coelacant1/EpsilonProtogen/Pictures/1 (1).jpg

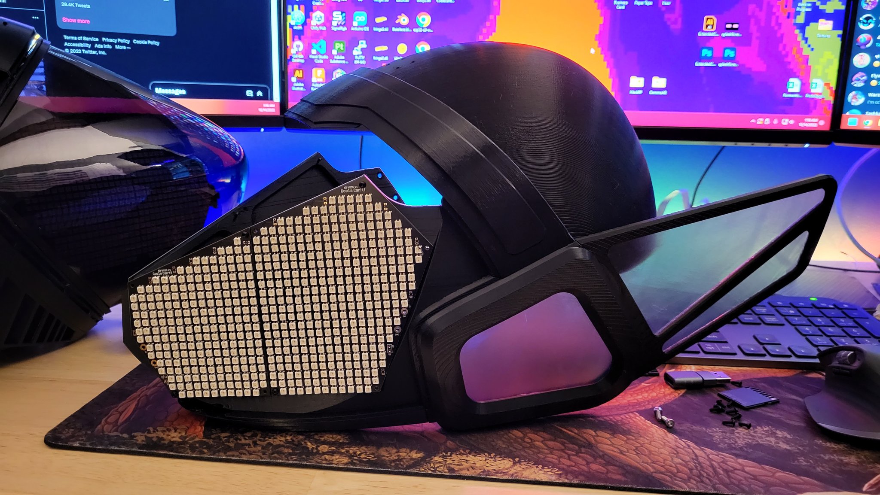
Pictures/1 (1).jpg
