coelacant1/EpsilonProtogen/Pictures/1 (2).jpg

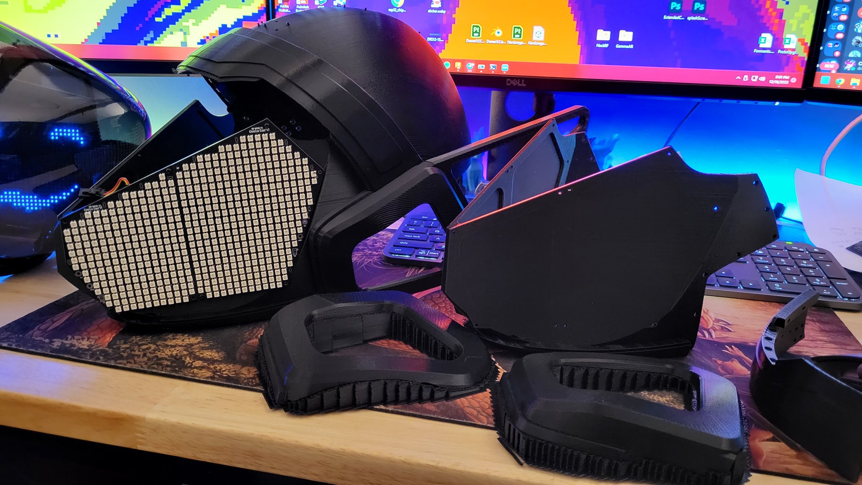
Pictures/1 (2).jpg
