coelacant1/EpsilonProtogen/Pictures/1 (3).jpg

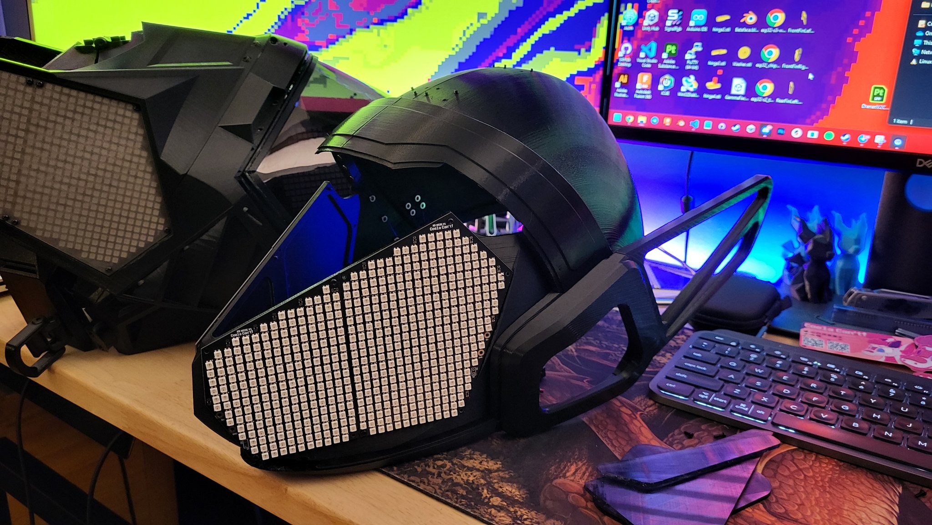
Pictures/1 (3).jpg
