coelacant1/EpsilonProtogen/Pictures/Bottom.png

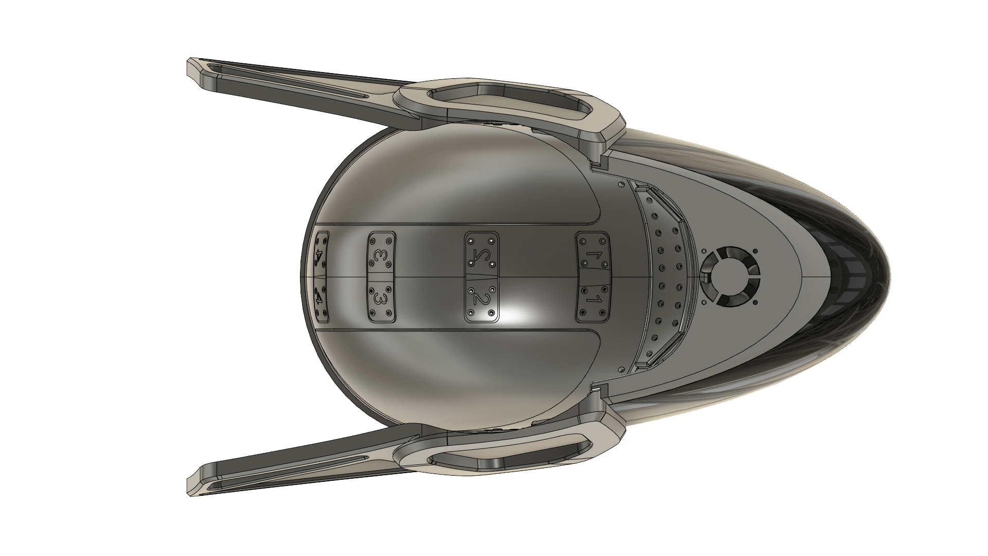
Pictures/Bottom.png
