coelacant1/EpsilonProtogen/Pictures/Edges.png

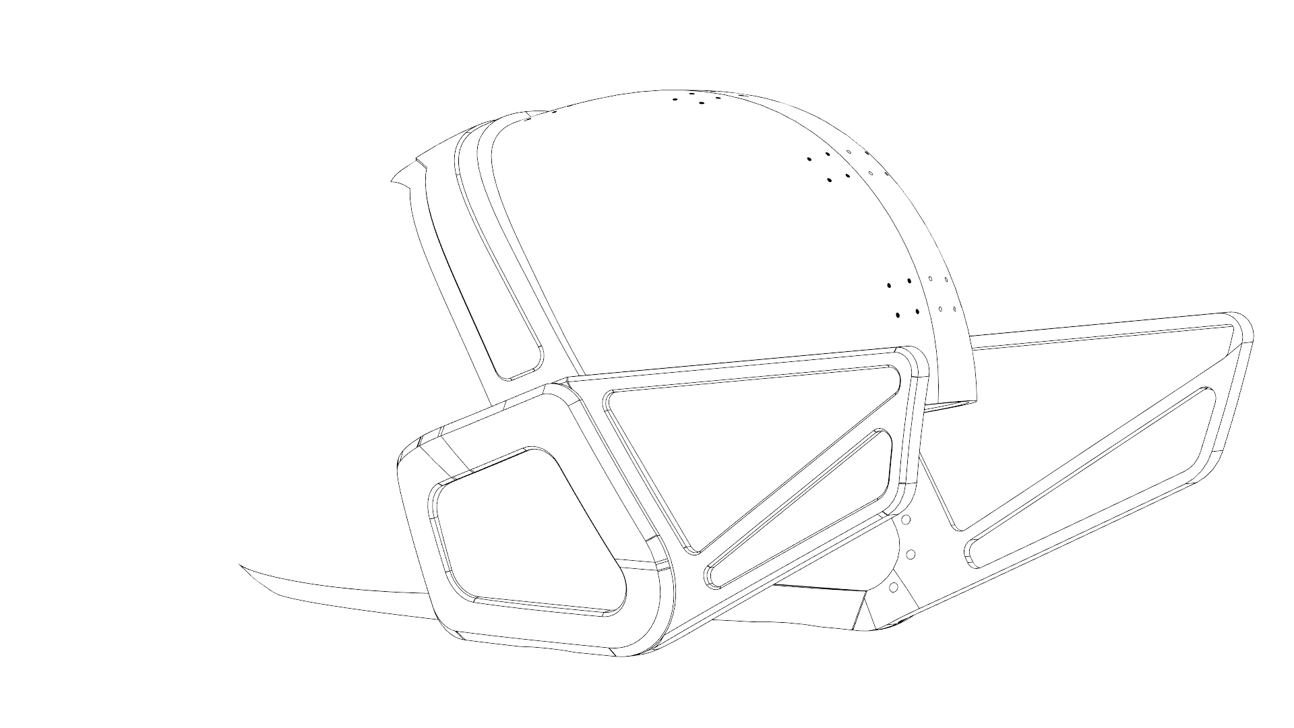
Pictures/Edges.png
