coelacant1/EpsilonProtogen/Pictures/Front.png

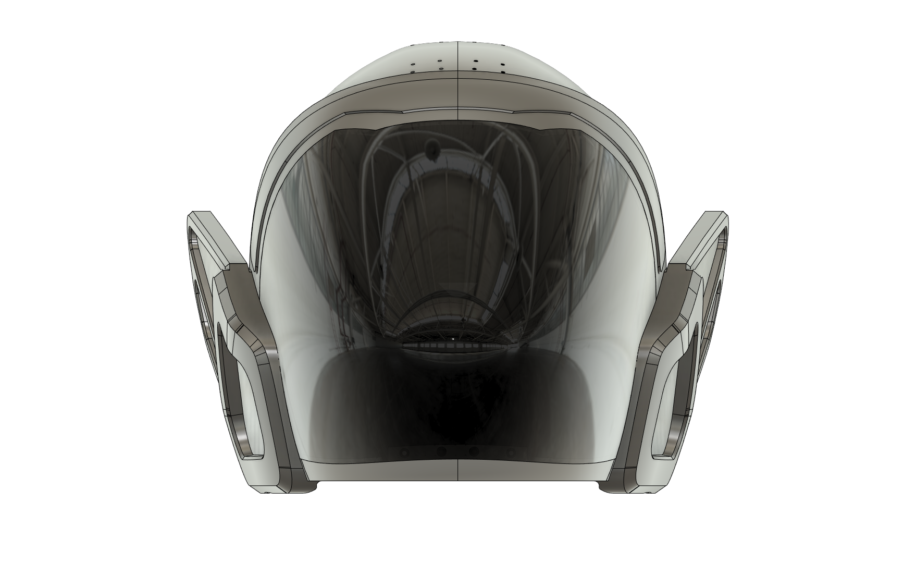
Pictures/Front.png
