coelacant1/EpsilonProtogen/Pictures/MAX7219.png

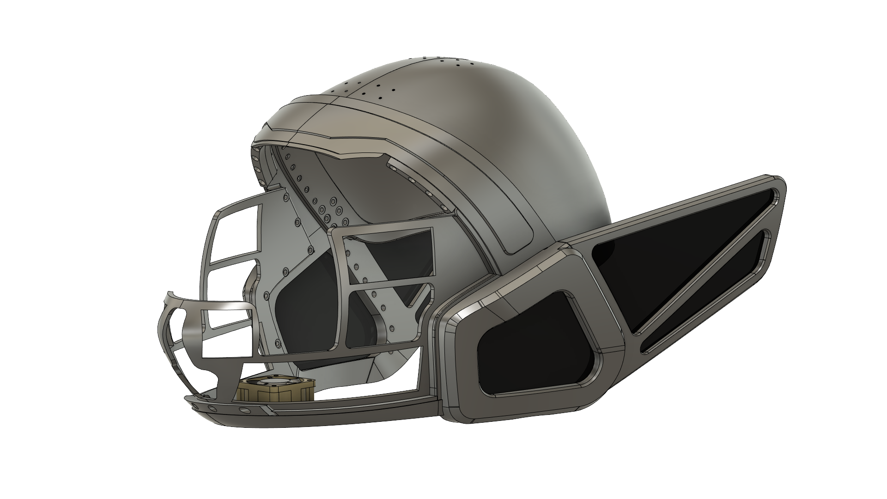
Pictures/MAX7219.png
