coelacant1/EpsilonProtogen/Pictures/VacuumBuck.png

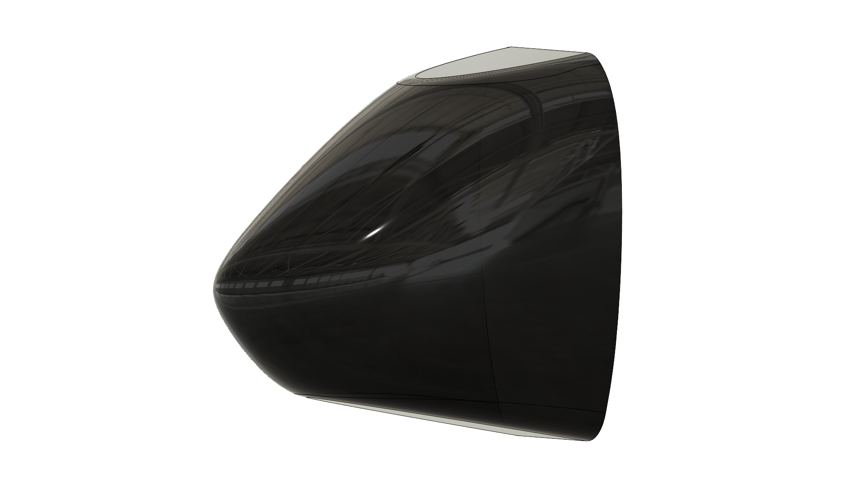
Pictures/VacuumBuck.png
