coelacant1/EpsilonProtogen/Frame Connectors/FrontHelmetJoin.stl

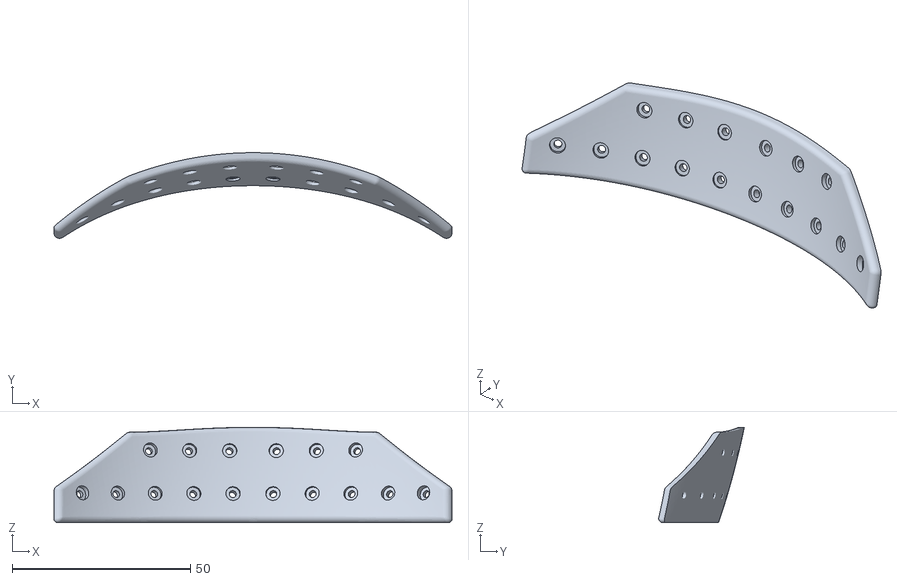
[picture p29: CAD file, 2023-06-29]
Frame Connectors/FrontHelmetJoin.stl
111.7 x 24.0 x 26.8
