coelacant1/EpsilonProtogen/Frame/Left/RearTopFinDisplay.stl

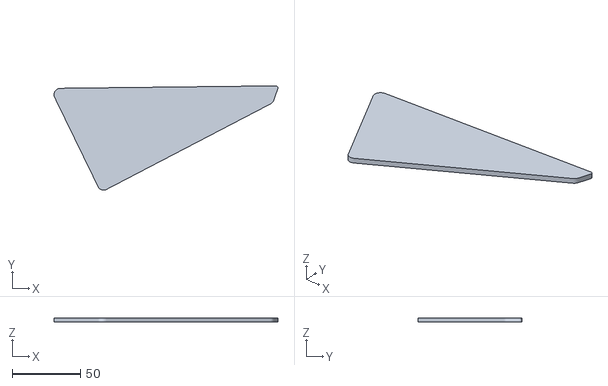
[picture p30: CAD file, 2023-06-29]
Frame/Left/RearTopFinDisplay.stl
164.5 x 76.6 x 3.29
