coelacant1/EpsilonProtogen/Frame Connectors/HelmetJoin3.stl

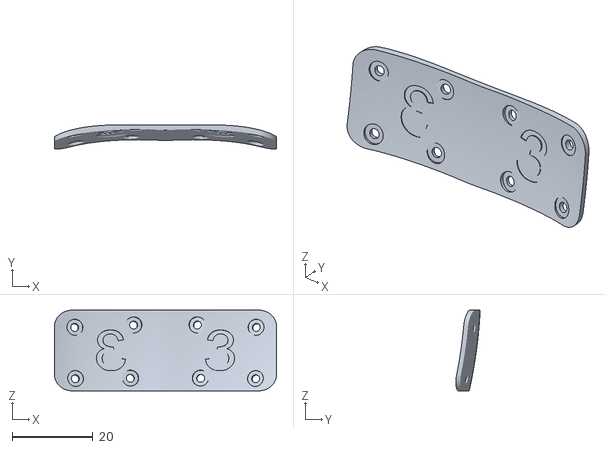
[picture p31: CAD file, 2023-06-29]
Frame Connectors/HelmetJoin3.stl
55.0 x 6.04 x 20.0
