coelacant1/EpsilonProtogen/Frame/Left/RearFinLeft.stl

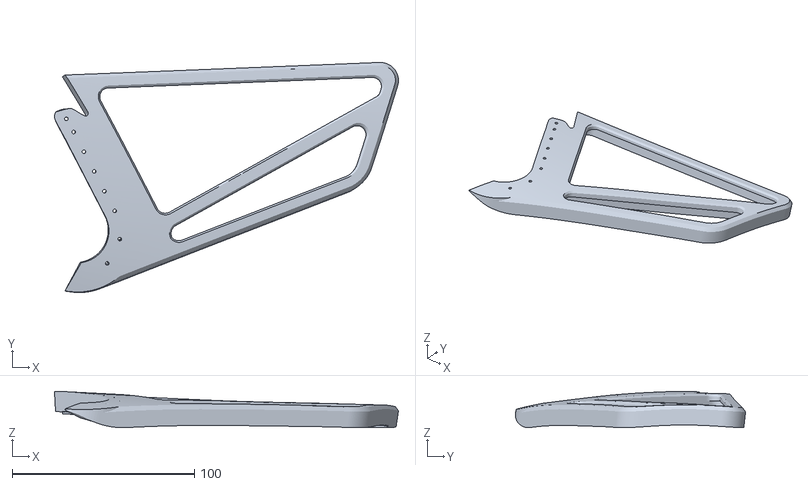
[picture p32: CAD file, 2023-06-29]
Frame/Left/RearFinLeft.stl
188.8 x 126.3 x 20.0
