coelacant1/EpsilonProtogen/Frame/Right/RearBottomFinDisplay.stl

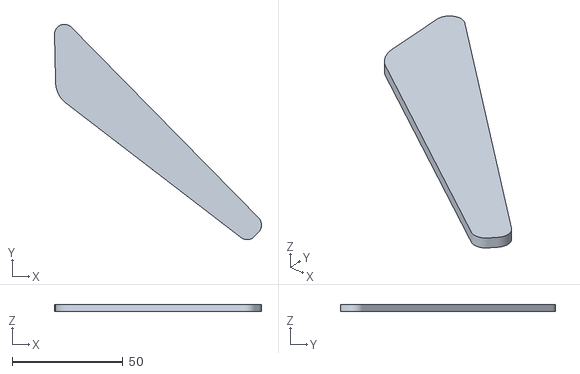
[picture p33: CAD file, 2023-06-29]
Frame/Right/RearBottomFinDisplay.stl
93.4 x 97.2 x 3.29
