coelacant1/EpsilonProtogen/Frame Connectors/HelmetJoin4.stl

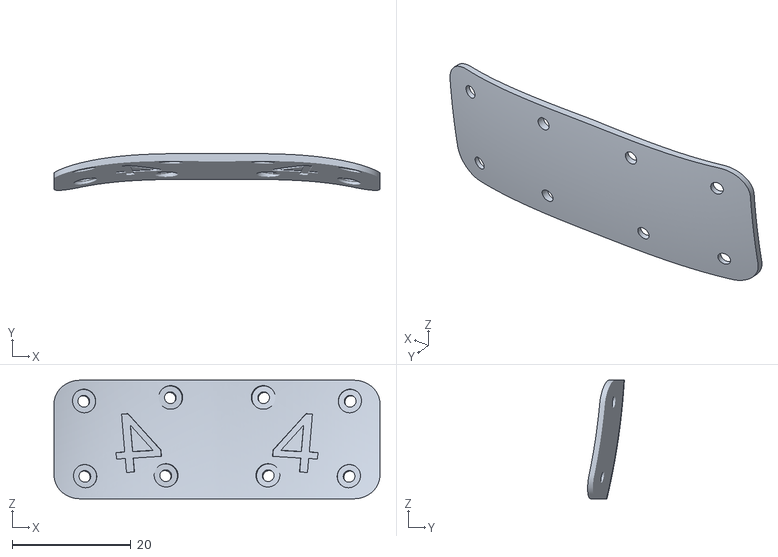
[picture p34: CAD file, 2023-06-29]
Frame Connectors/HelmetJoin4.stl
55.0 x 6.21 x 20.0
